holmesrichards/pmf/Images/pmf_panel_holes.png

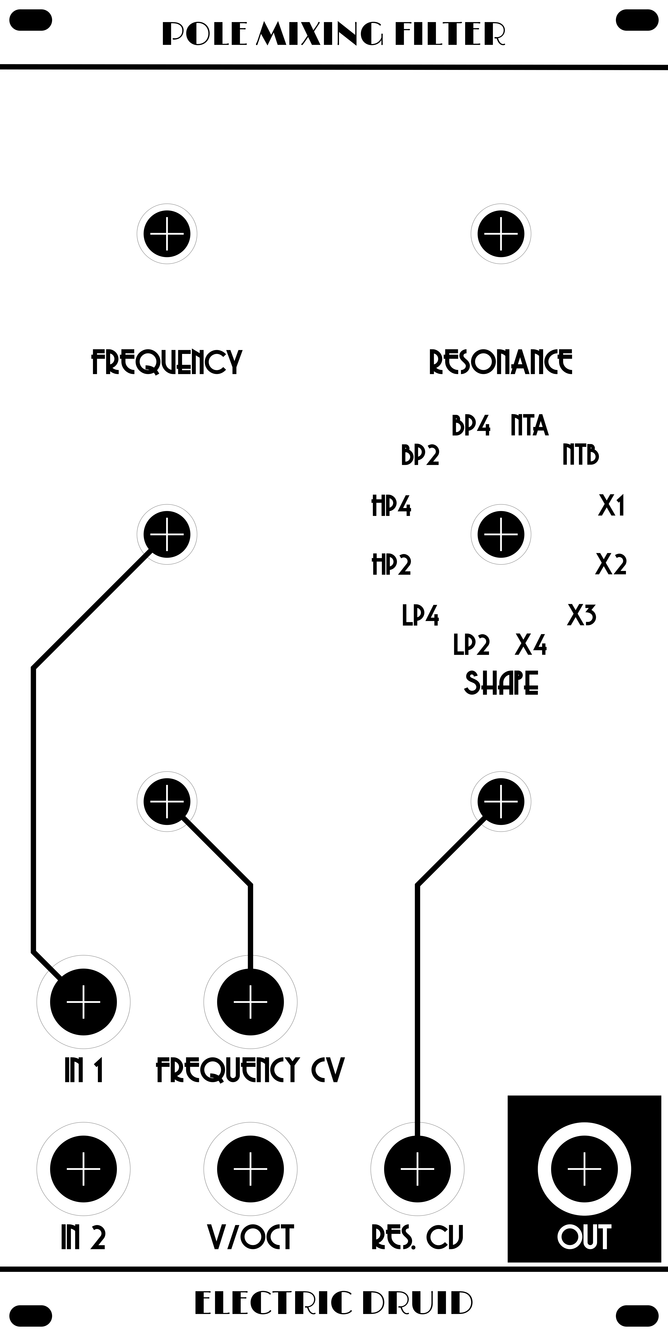
Images/pmf_panel_holes.png
