holmesrichards/pmf/Docs/Layout/pmf_daughter/pmf_daughter_B.SilkS.pdf

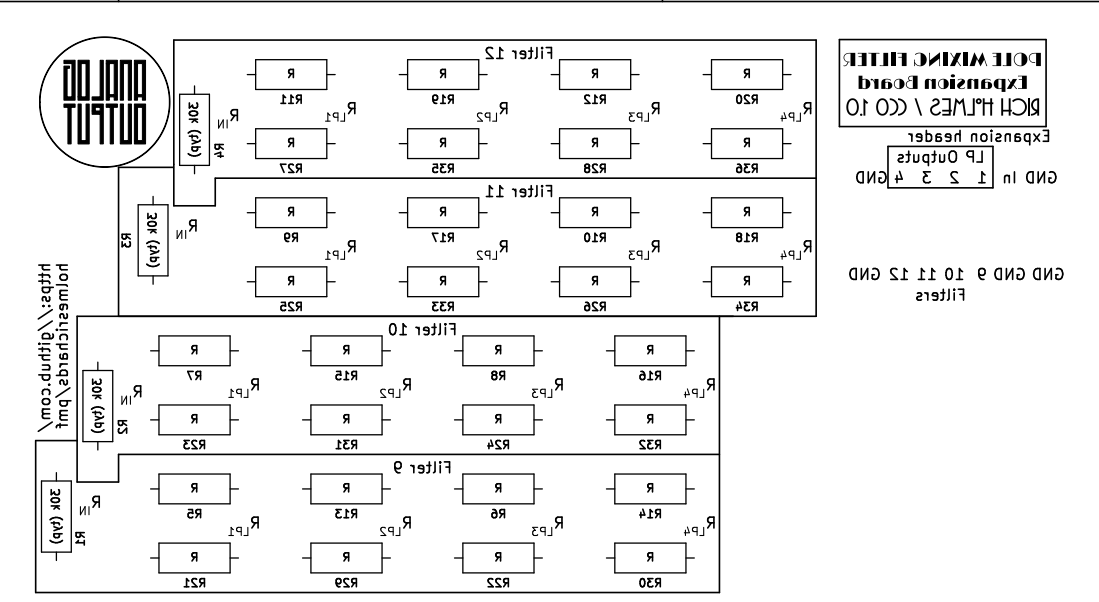
[picture p38: page 1]

LP1 10 GND POLE MIXING FILTER

LP Outputs R https://github.com/ holmesrichards/pmf R
