holmesrichards/pmf/Docs/Layout/pmf_B2/pmf_B2_B.Mask.pdf

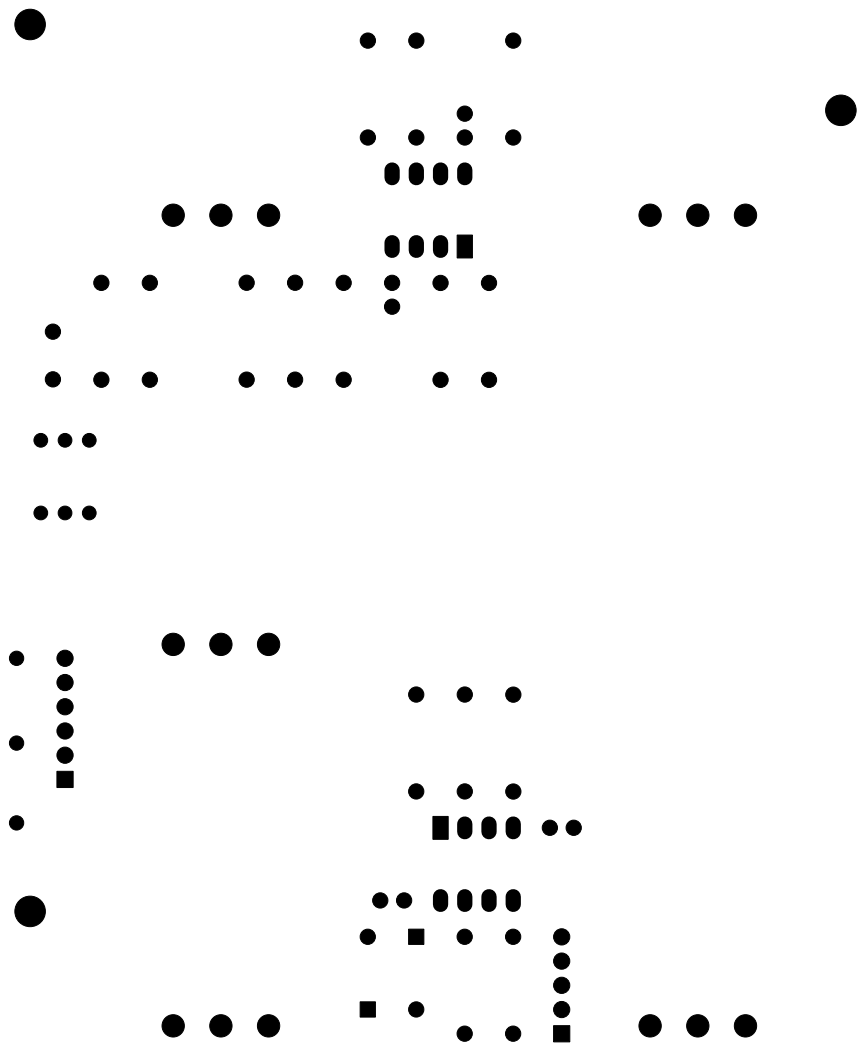
[picture p47: page 1]
