holmesrichards/pmf/Docs/Layout/pmf_B2/pmf_B2_B.Paste.pdf

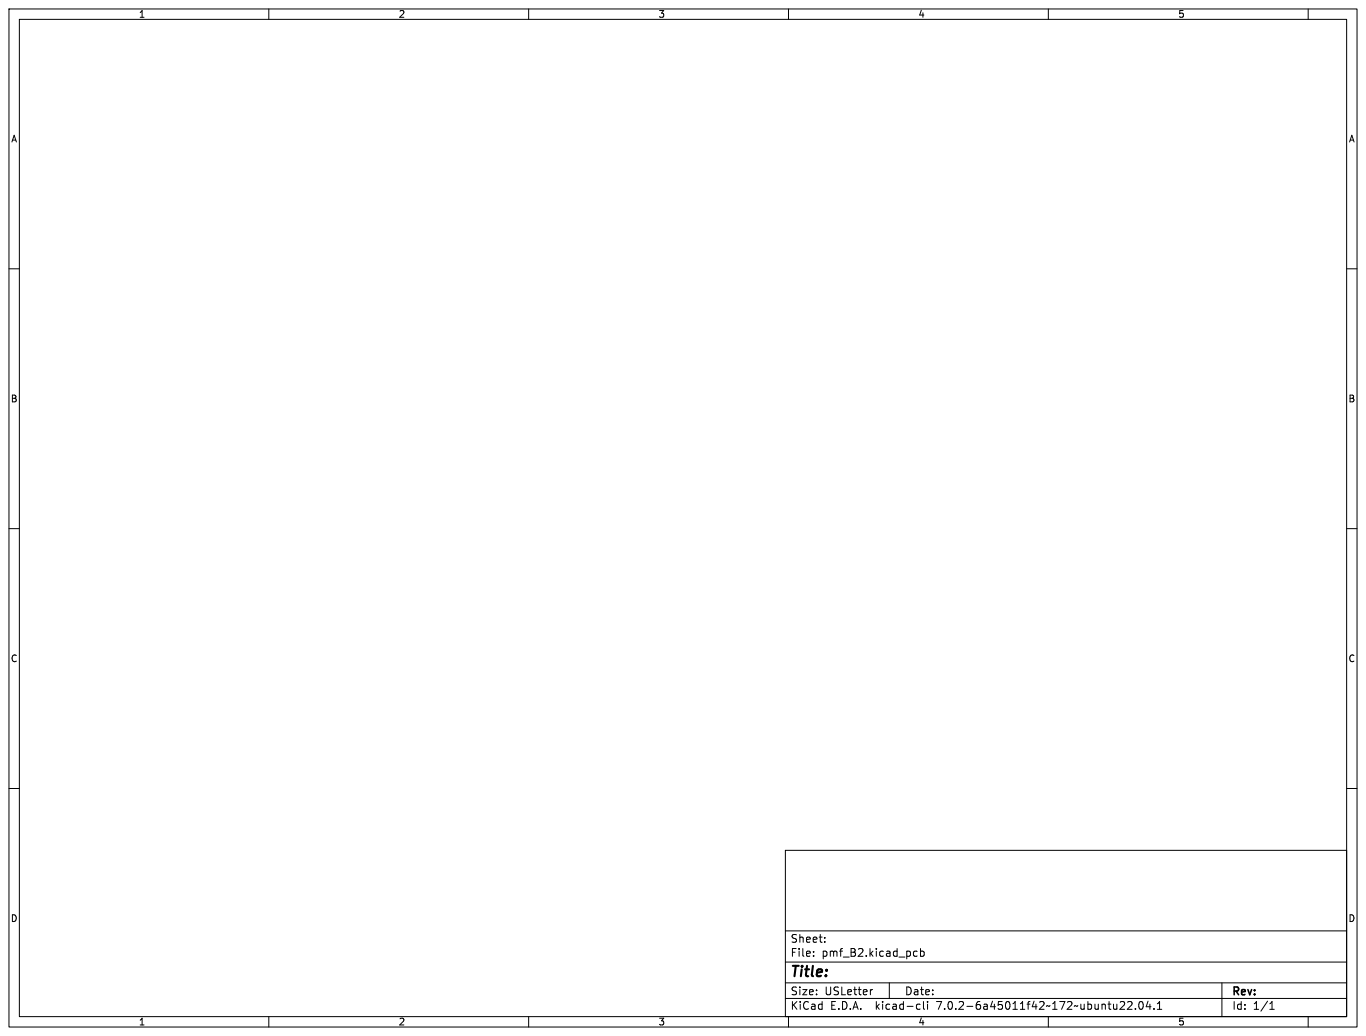
[picture p48: page 1]
