holmesrichards/pmf/Docs/Layout/pmf_B2/pmf_B2_B.SilkS.pdf

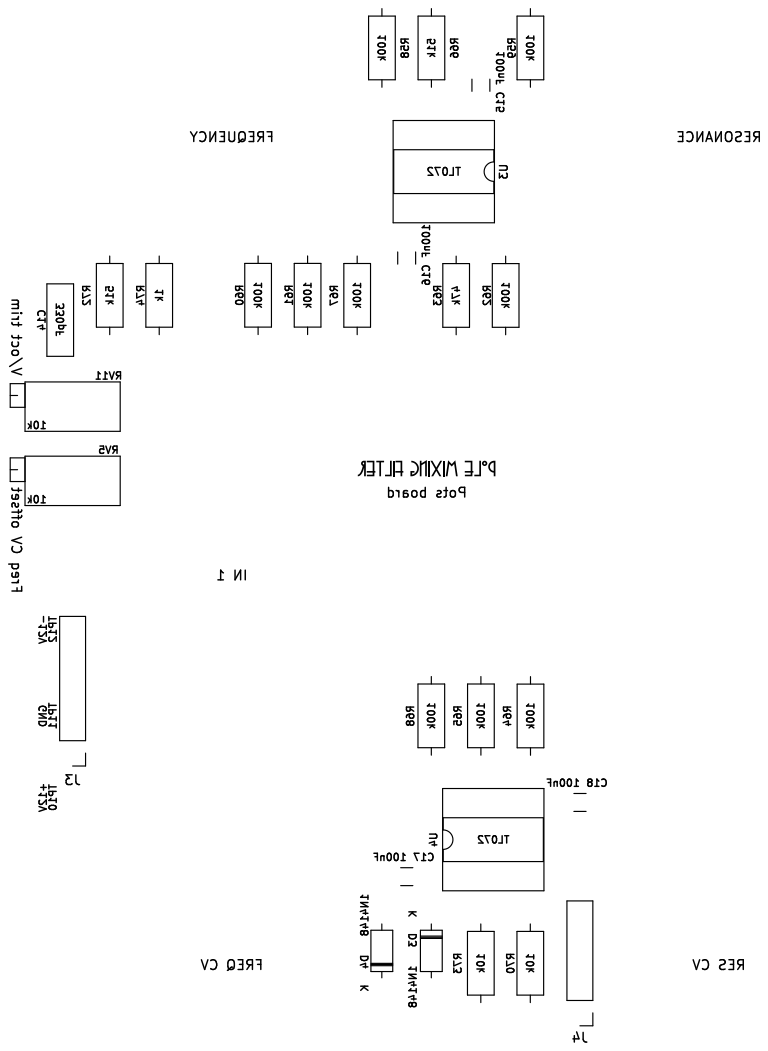
[picture p49: page 1]
