holmesrichards/pmf/Docs/Layout/pmf_B2/pmf_B2_Edge.Cuts.pdf

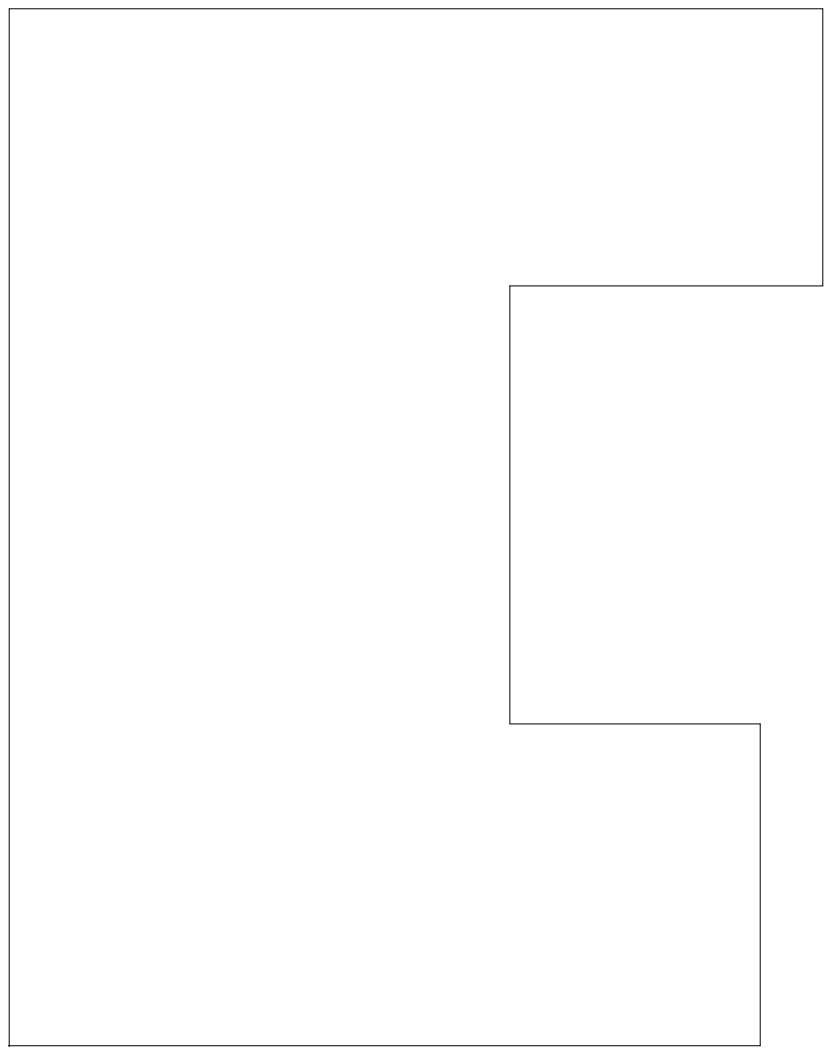
[picture p50: page 1]
