holmesrichards/pmf/Docs/Layout/pmf_B2/pmf_B2_F.Cu.pdf

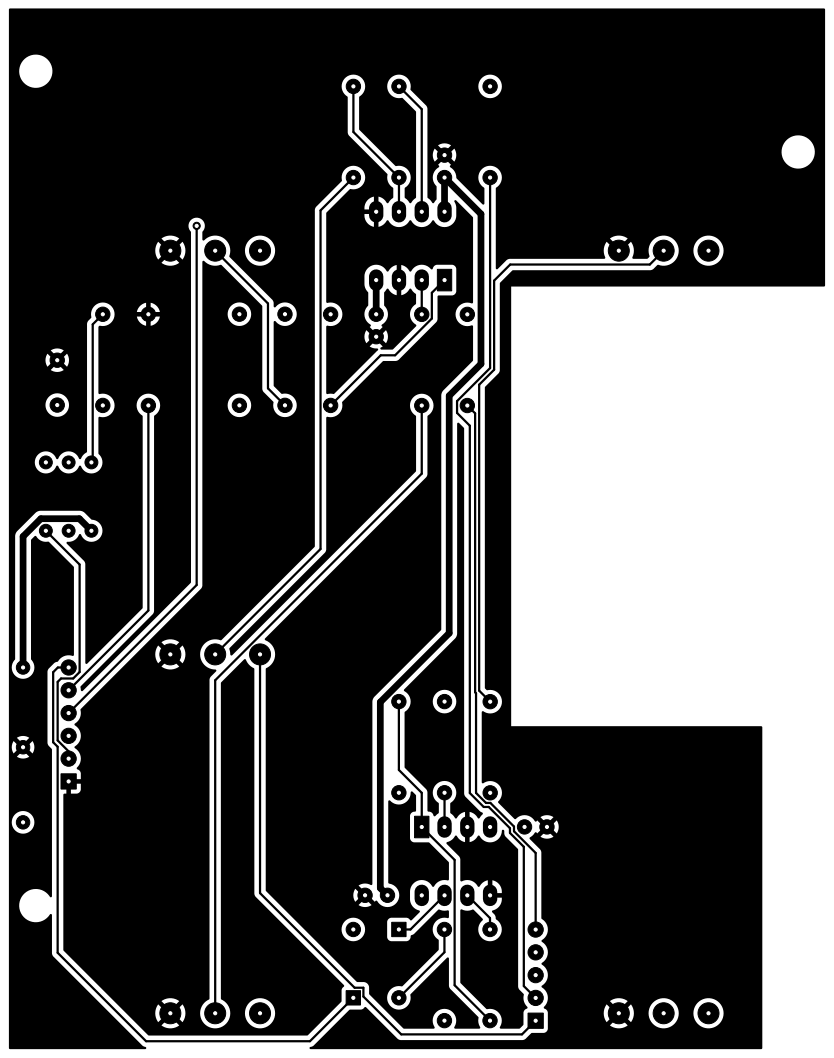
[picture p51: page 1]
