holmesrichards/pmf/Docs/Layout/pmf_B2/pmf_B2_F.SilkS.pdf

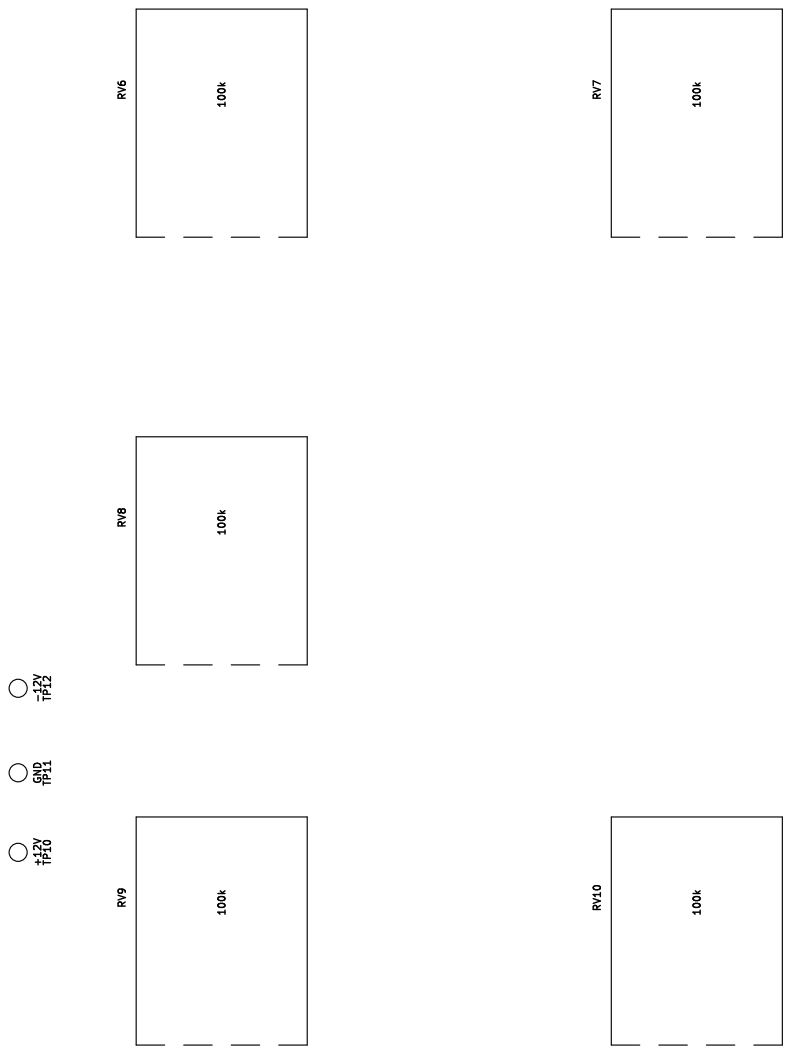
[picture p52: page 1]
