holmesrichards/pmf/Docs/Layout/pmf_panel/pmf_panel_B.Cu.pdf

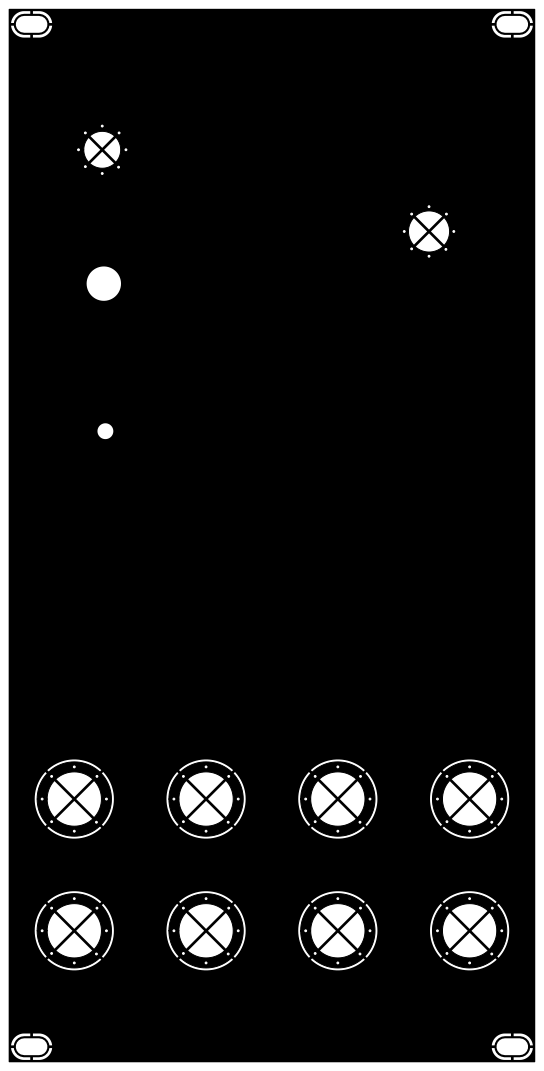
[picture p53: page 1]
