holmesrichards/pmf/Docs/Layout/pmf_panel/pmf_panel_B.Mask.pdf

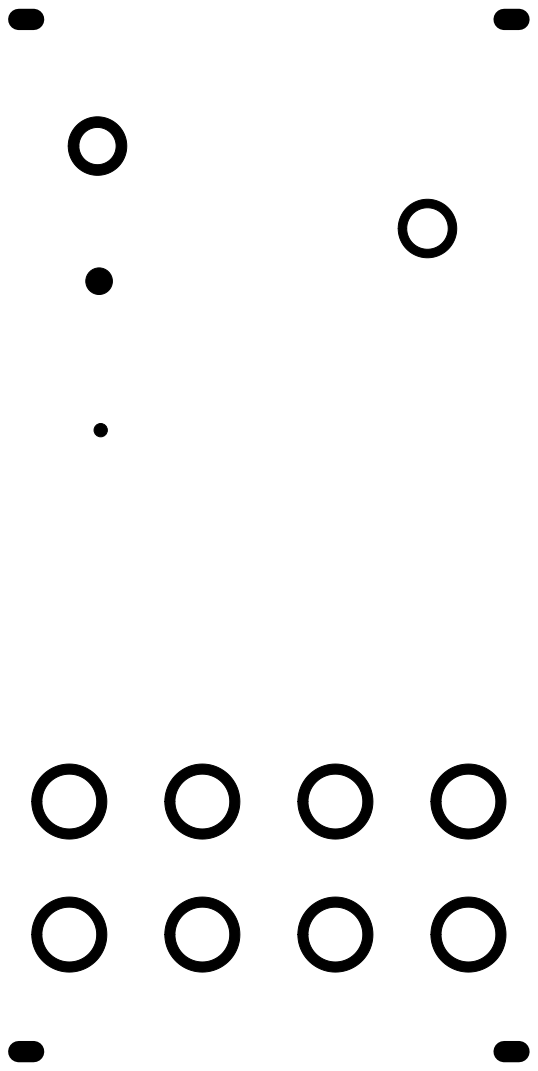
[picture p54: page 1]
