holmesrichards/pmf/Docs/Layout/pmf_panel/pmf_panel_B.Paste.pdf

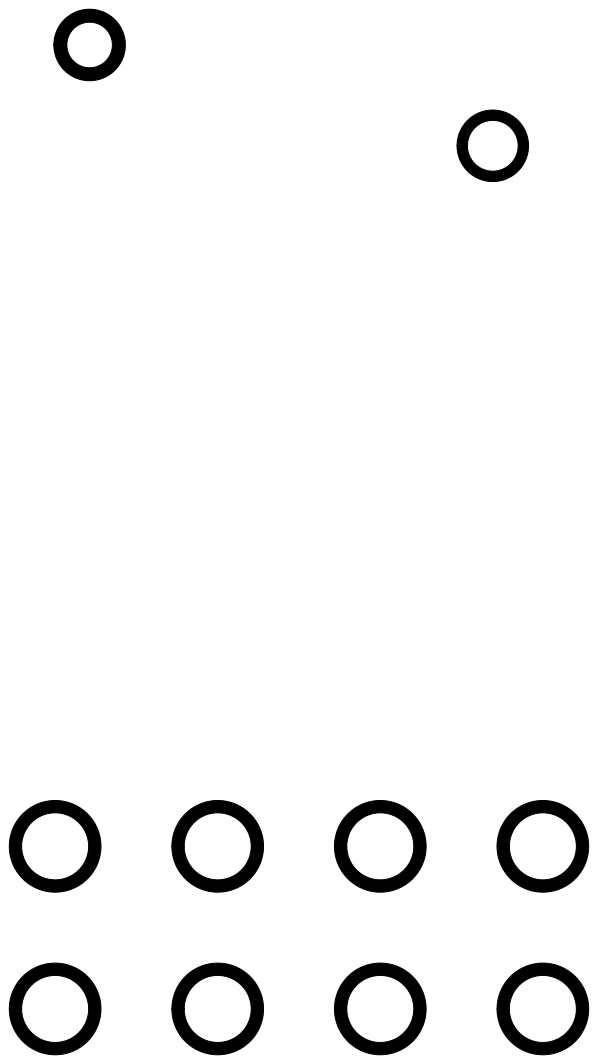
[picture p55: page 1]
