holmesrichards/pmf/Docs/Layout/pmf_panel/pmf_panel_B.SilkS.pdf

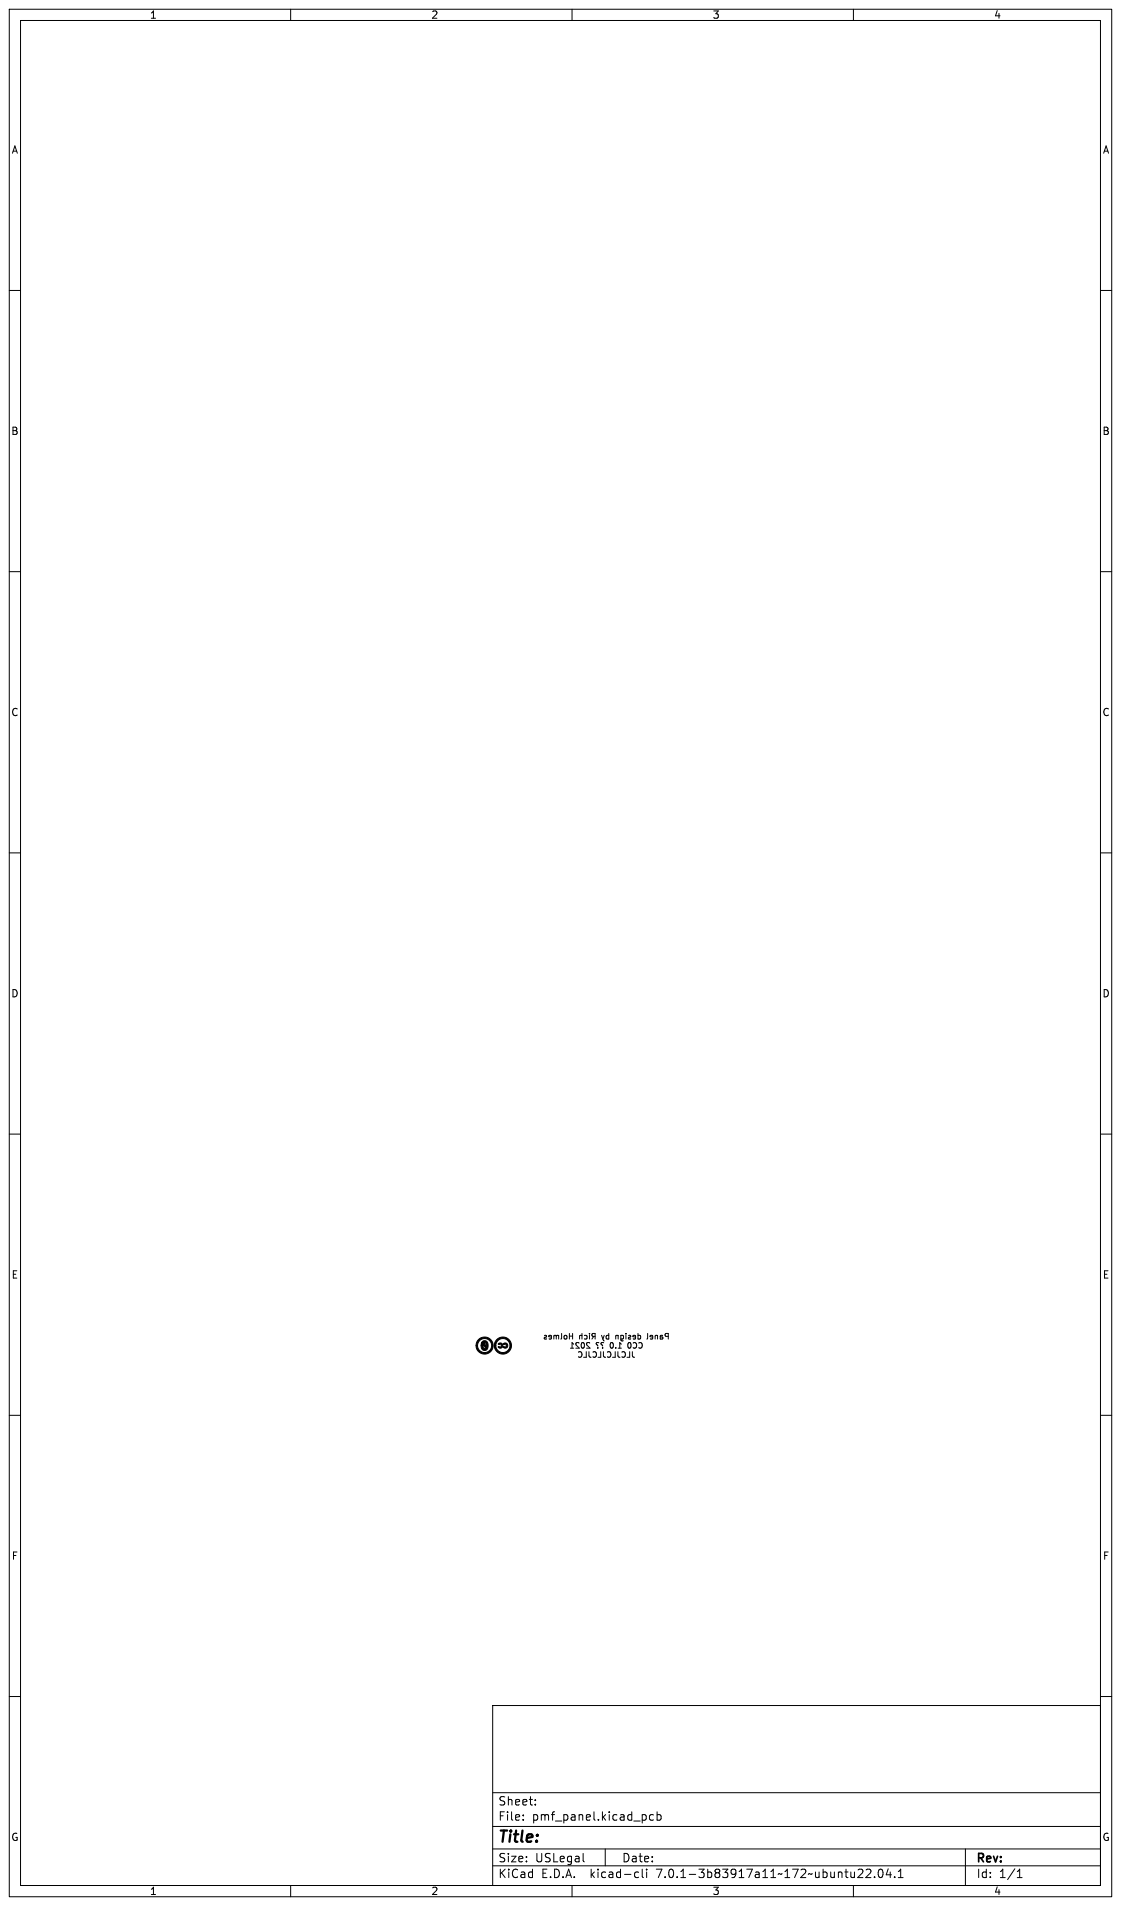
[picture p56: page 1]

Panel design by Rich Holmes CC0 1.0 ?? 2021
