holmesrichards/pmf/Docs/Layout/pmf_panel/pmf_panel_Edge.Cuts.pdf

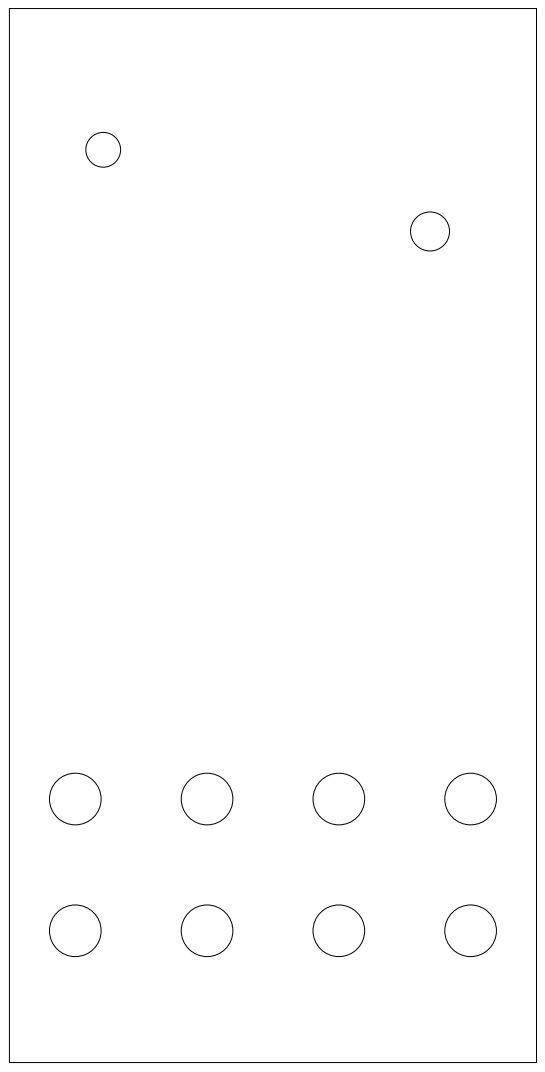
[picture p57: page 1]
