holmesrichards/pmf/Docs/Layout/pmf_panel/pmf_panel_F.SilkS.pdf

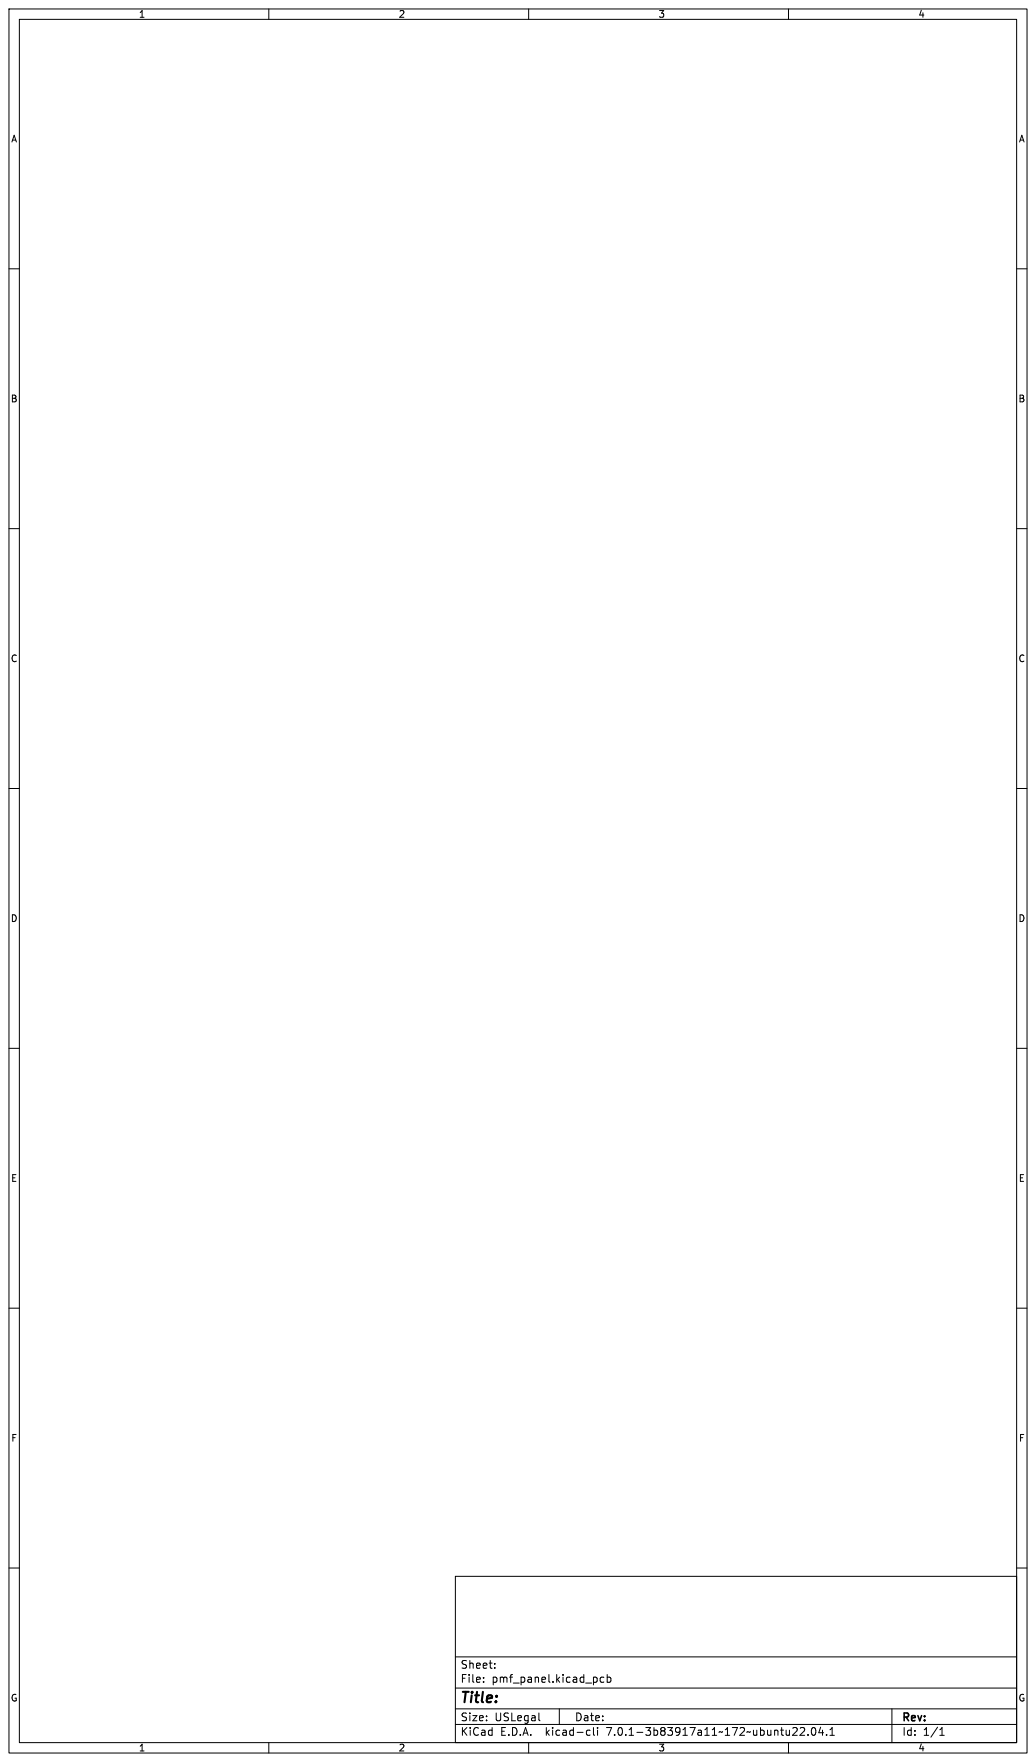
[picture p58: page 1]
