holmesrichards/pmf/Docs/Layout/pmf_daughter/pmf_daughter_B.Cu.pdf

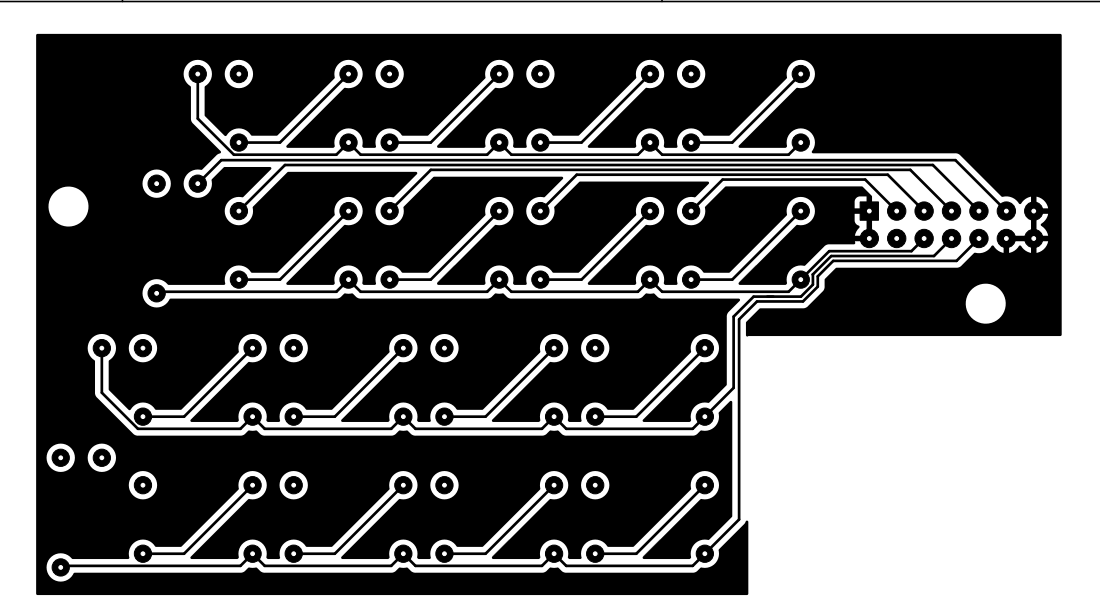
[picture p59: page 1]
