holmesrichards/pmf/Docs/Layout/pmf_daughter/pmf_daughter_B.Mask.pdf

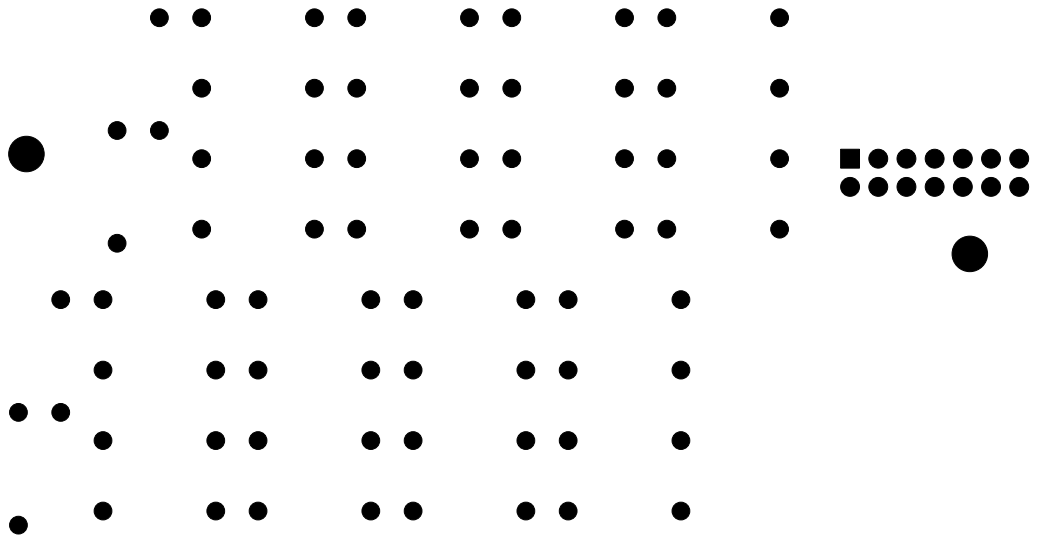
[picture p60: page 1]
