holmesrichards/pmf/Docs/Layout/pmf_daughter/pmf_daughter_B.Paste.pdf

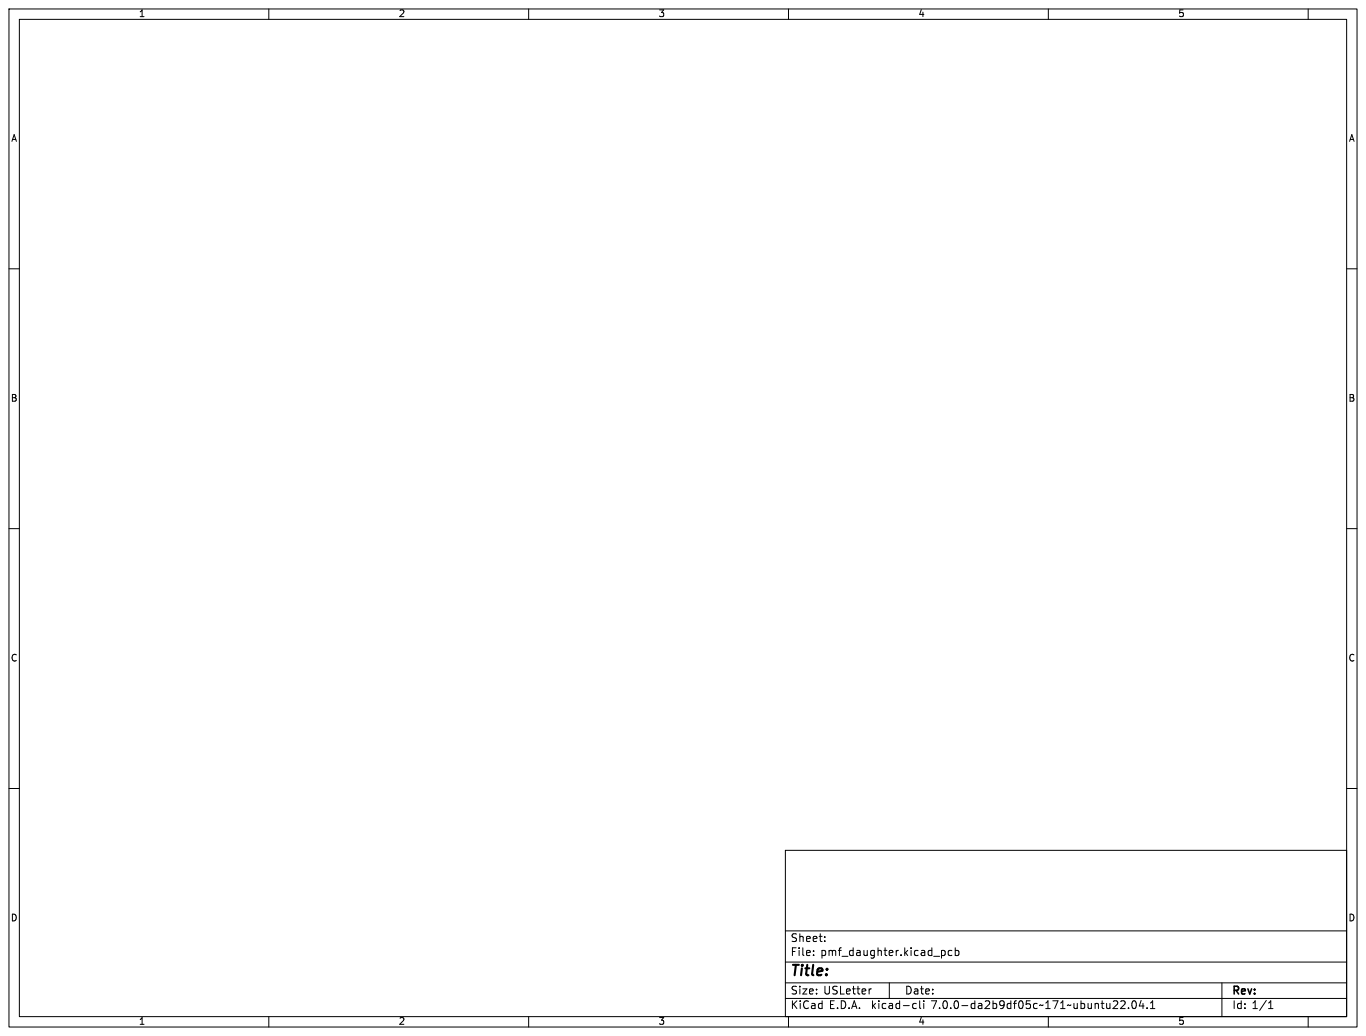
[picture p61: page 1]
