holmesrichards/pmf/Docs/Layout/pmf_daughter/pmf_daughter_Edge.Cuts.pdf

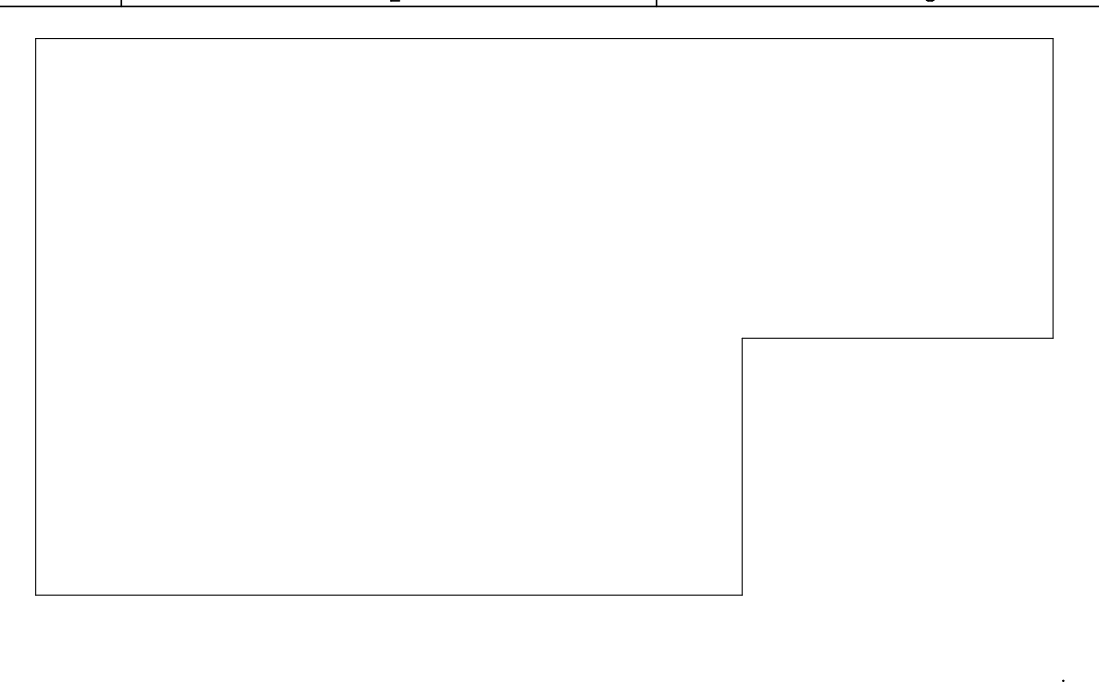
[picture p62: page 1]
