holmesrichards/pmf/Docs/Layout/pmf_daughter/pmf_daughter_F.Cu.pdf

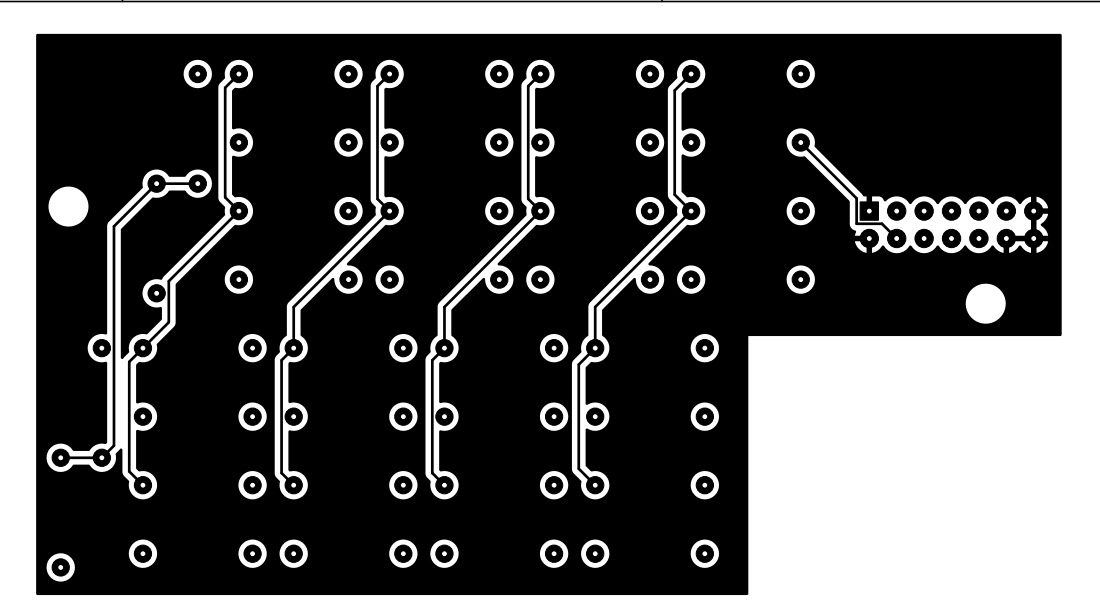
[picture p63: page 1]
