holmesrichards/pmf/Docs/Layout/pmf_daughter/pmf_daughter_F.SilkS.pdf

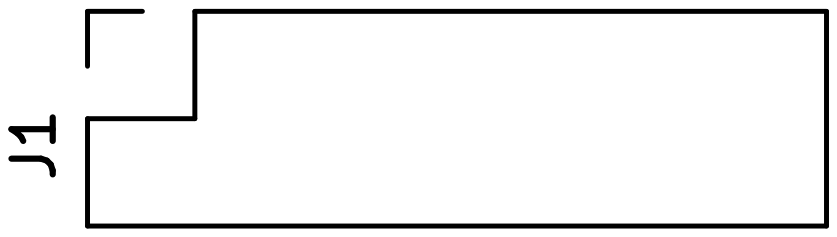
[picture p64: page 1]
